StrawsonDesign/Ultimaker2-Feeder-Reversal/Parts/Fan Duct/solidworks assembly/1329-B2P-C Dual Fan Bracket.STEP

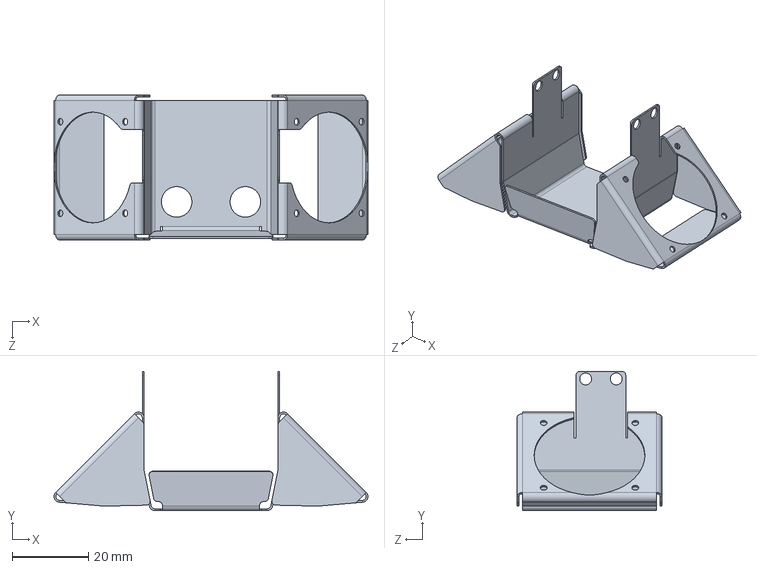
[picture p28: CAD file, 2015-10-15]
Parts/Fan Duct/solidworks assembly/1329-B2P-C Dual Fan Bracket.STEP
82.2 x 36.5 x 38.0 mm
