StrawsonDesign/Ultimaker2-Feeder-Reversal/Parts/Bearing Filament Guides/Clip.stl

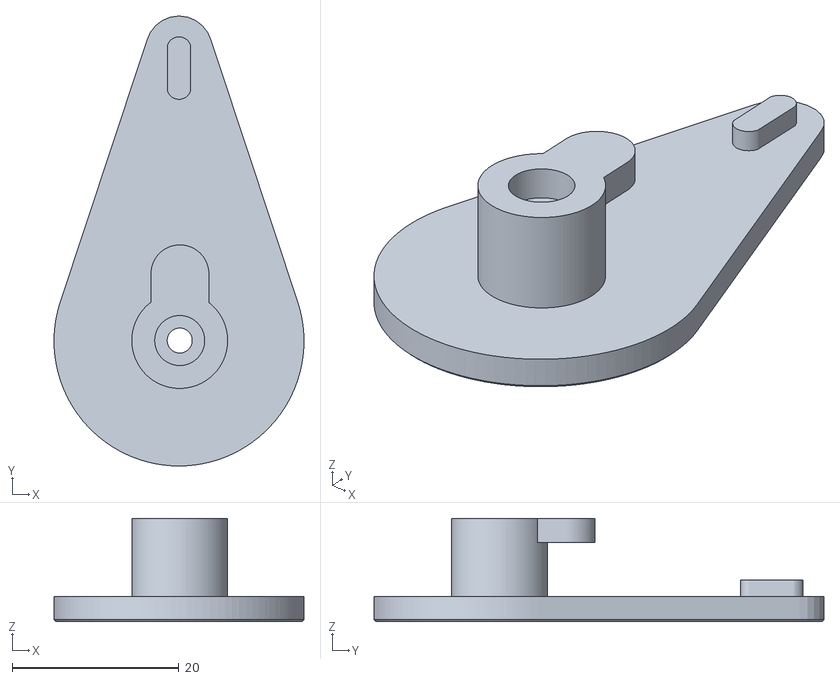
[picture p29: CAD file, 2015-10-15]
Parts/Bearing Filament Guides/Clip.stl
30.0 x 54.0 x 12.4
