StrawsonDesign/Ultimaker2-Feeder-Reversal/Parts/Fan Duct/solidworks assembly/1330-Z1P-B Cooling Fan.STEP

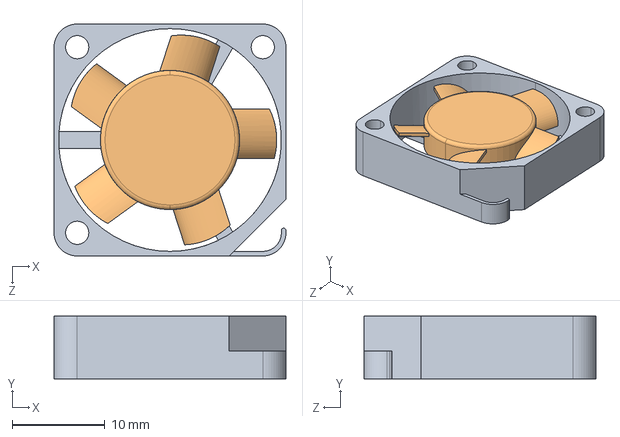
[picture p30: CAD file, 2015-10-15]
Parts/Fan Duct/solidworks assembly/1330-Z1P-B Cooling Fan.STEP
25.0 x 6.75 x 25.0 mm
1330 Fan Base 25x25
1330 Fan Rotor 25x25
