StrawsonDesign/Ultimaker2-Feeder-Reversal/Parts/Fan Duct/solidworks assembly/Duct.SLDPRT

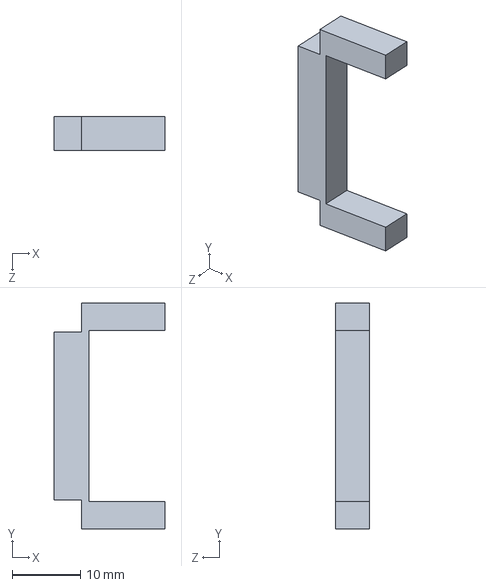
[picture p31: CAD file, 2015-10-15]
Parts/Fan Duct/solidworks assembly/Duct.SLDPRT
16.2 x 33.0 x 5.00 mm
